Markahofmeister/Whipper-Snapper/figures/cable-diagram-1.png

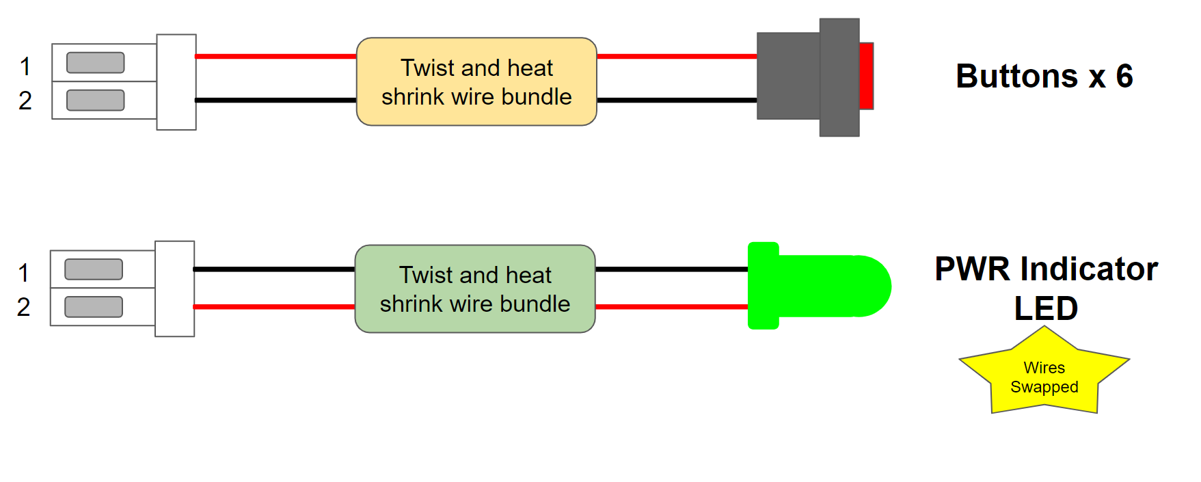
figures/cable-diagram-1.png
