Markahofmeister/Whipper-Snapper/figures/cable-diagram-2.png

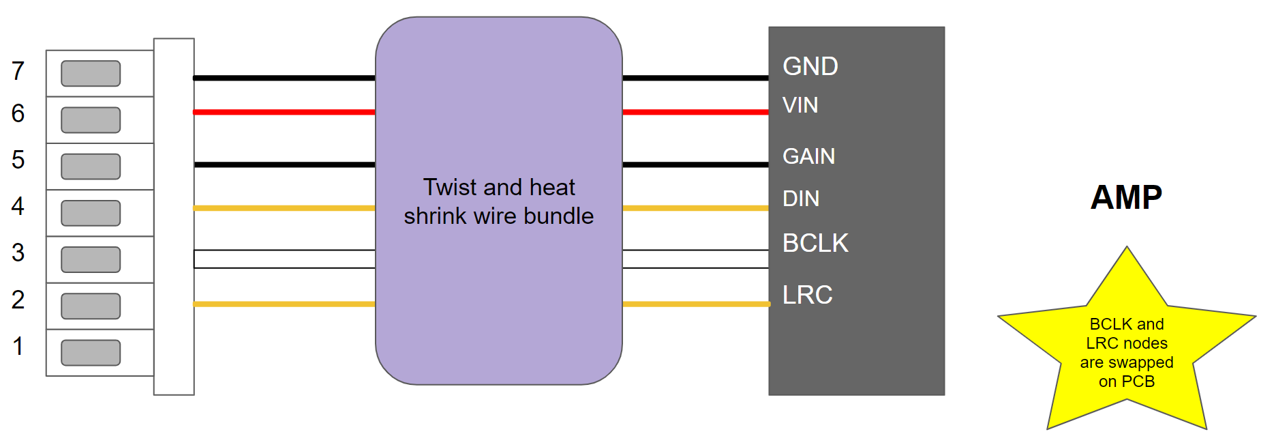
figures/cable-diagram-2.png
