Markahofmeister/Whipper-Snapper/figures/flowchart-interrupts.png

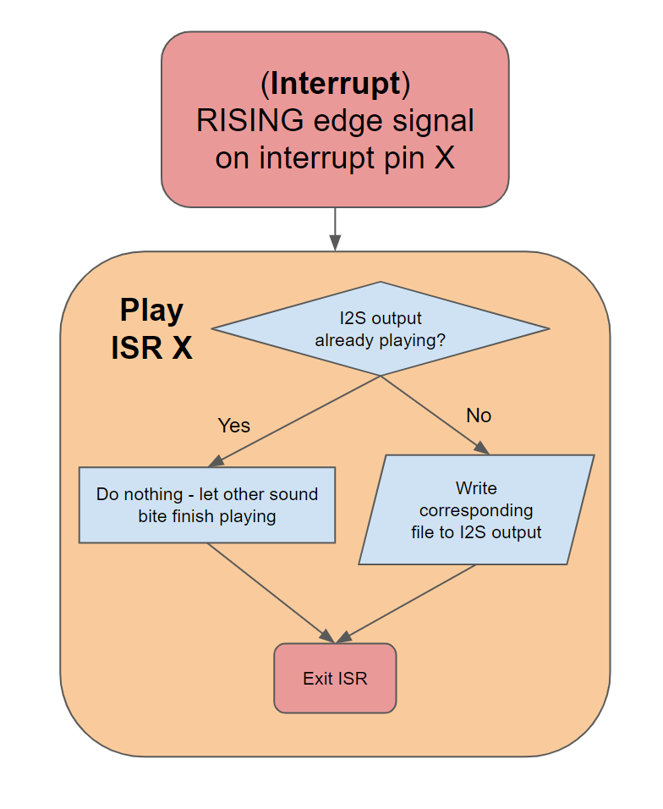
figures/flowchart-interrupts.png
