Markahofmeister/Whipper-Snapper/figures/flowchart-main.png

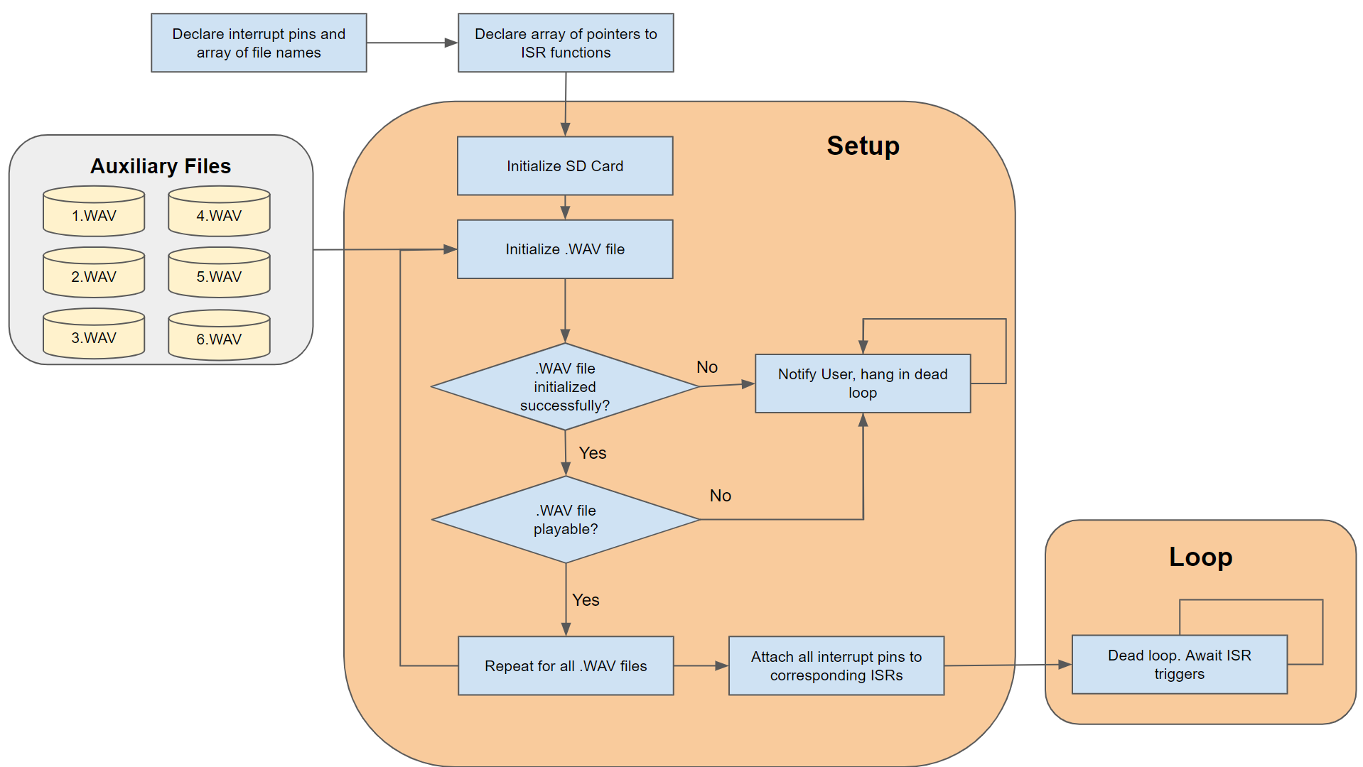
figures/flowchart-main.png
