Markahofmeister/Whipper-Snapper/media/amp.png

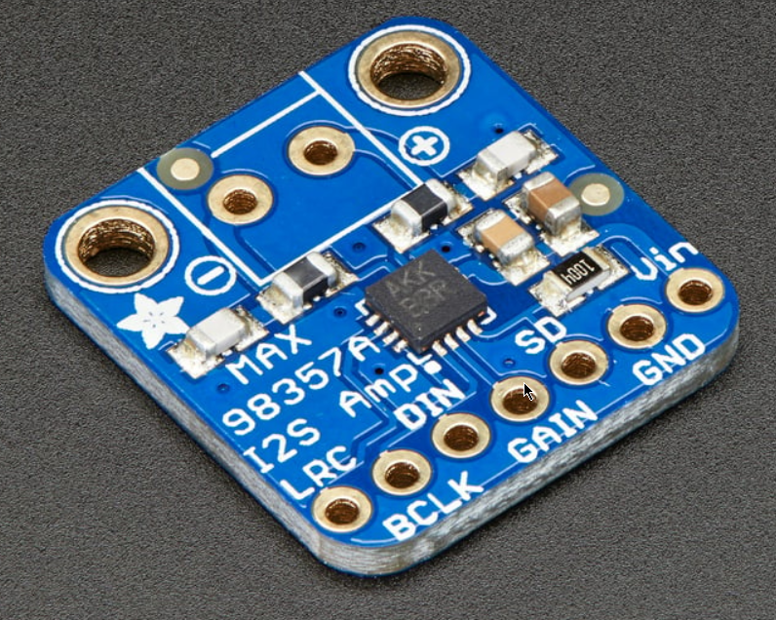
media/amp.png
