Markahofmeister/Whipper-Snapper/media/enclosure-layout-annotated.png

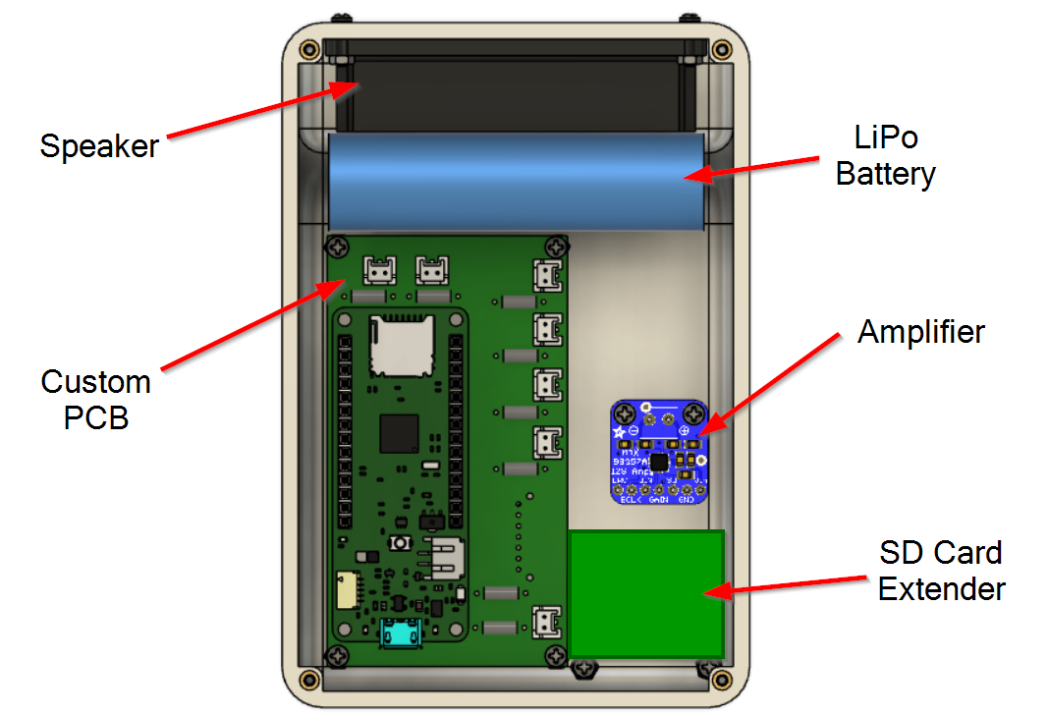
media/enclosure-layout-annotated.png
