Markahofmeister/Whipper-Snapper/media/exploded-view-annotated.png

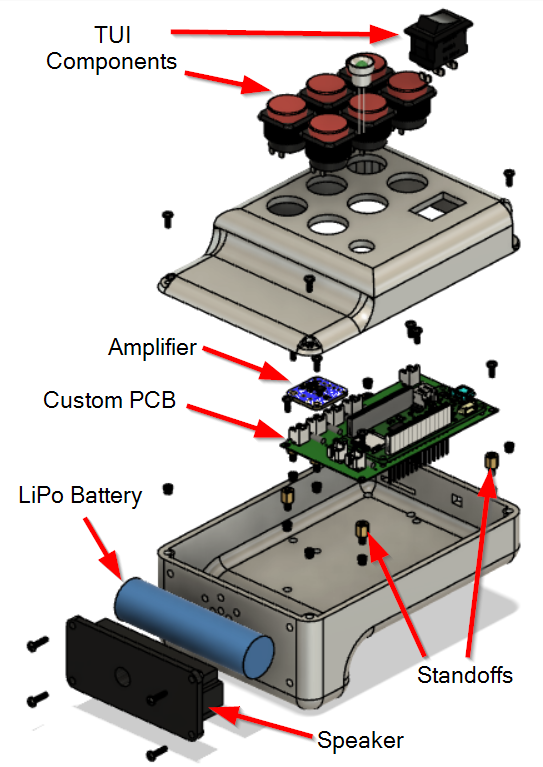
media/exploded-view-annotated.png
