Markahofmeister/Whipper-Snapper/media/final-1.jpg

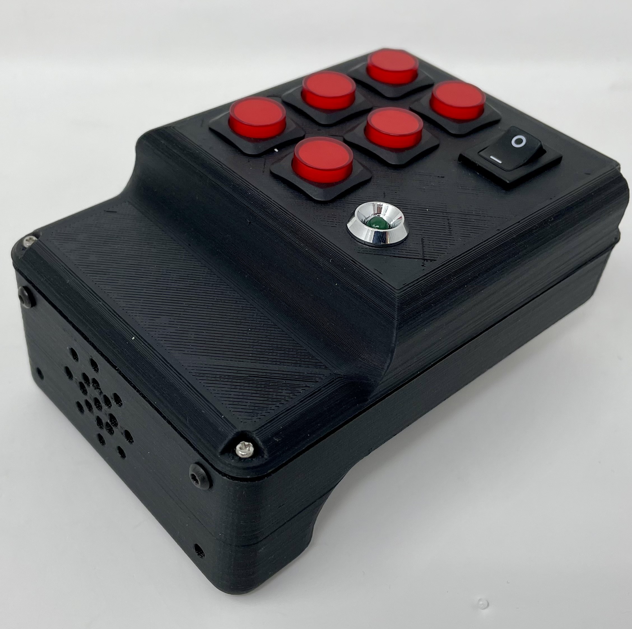
media/final-1.jpg
