Markahofmeister/Whipper-Snapper/media/fritzing.png

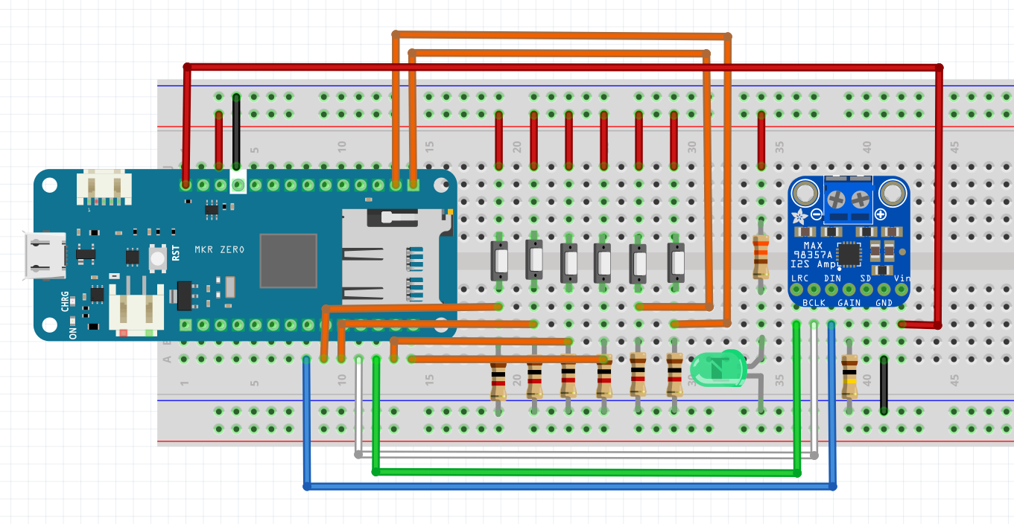
media/fritzing.png
