Markahofmeister/Whipper-Snapper/media/mkr-zero.png

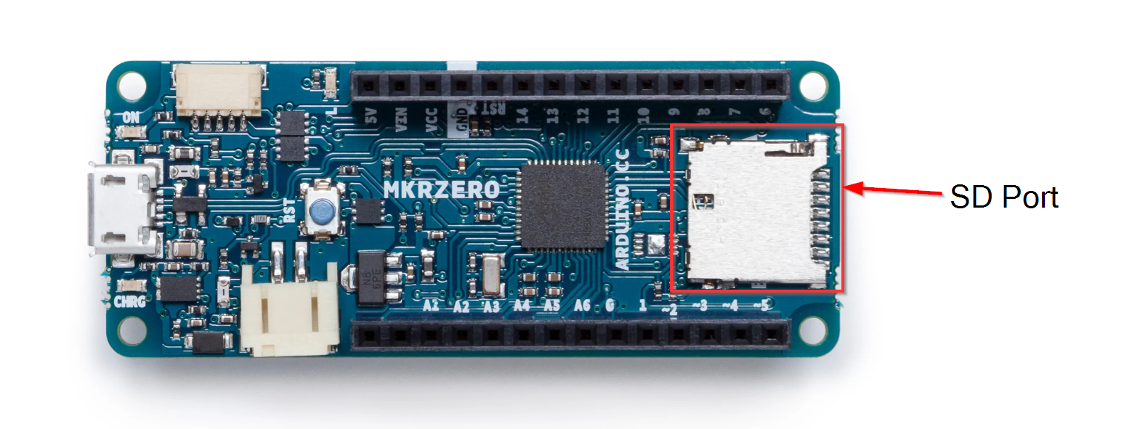
media/mkr-zero.png
