Markahofmeister/Whipper-Snapper/media/pcb-top.png

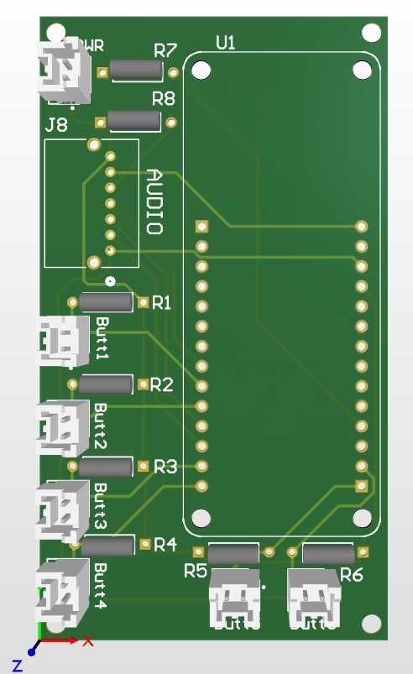
media/pcb-top.png
