Markahofmeister/Whipper-Snapper/media/ratsnest.jpg

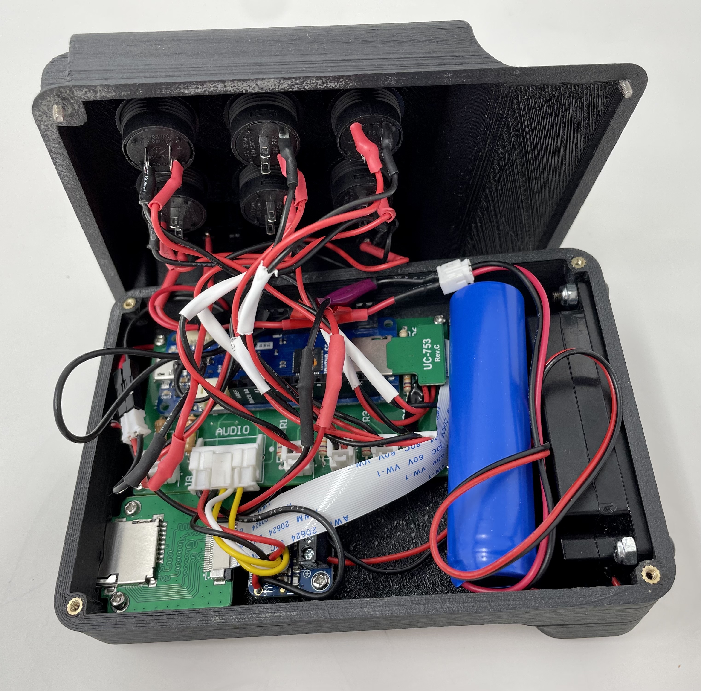
media/ratsnest.jpg
