Markahofmeister/Whipper-Snapper/media/render.png

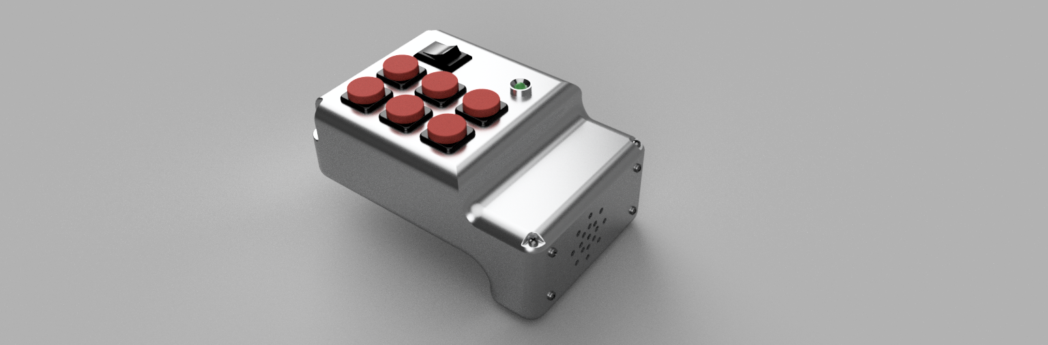
media/render.png
