Markahofmeister/Whipper-Snapper/media/SD-charger.jpg

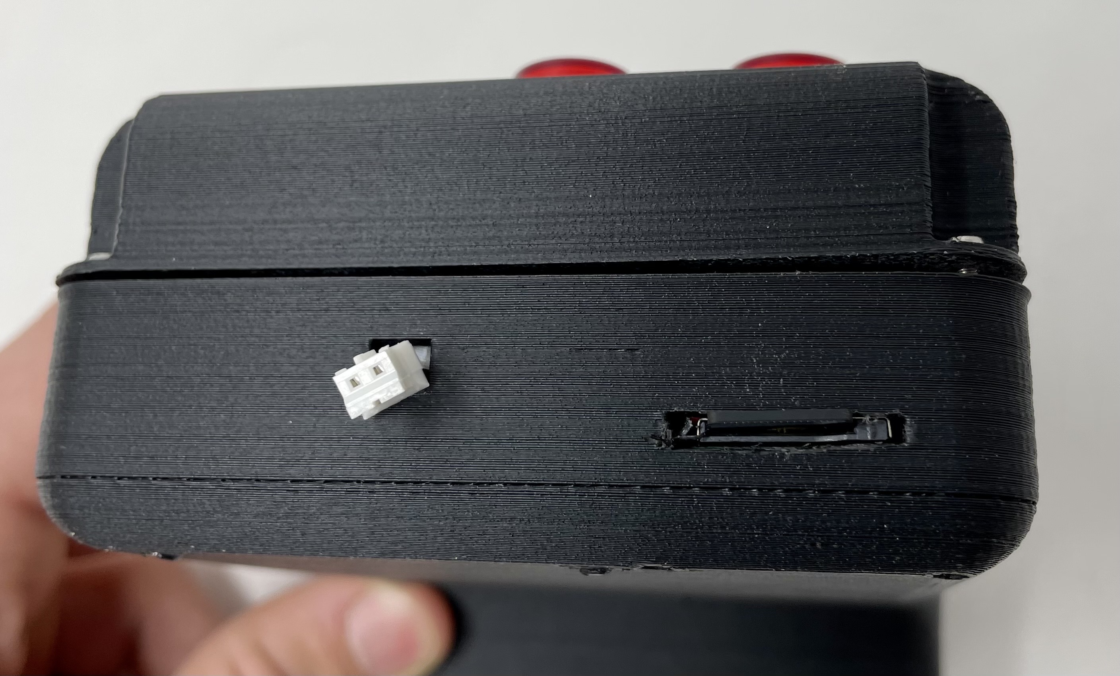
media/SD-charger.jpg
