Markahofmeister/Whipper-Snapper/media/SD-chrger-annotated.png

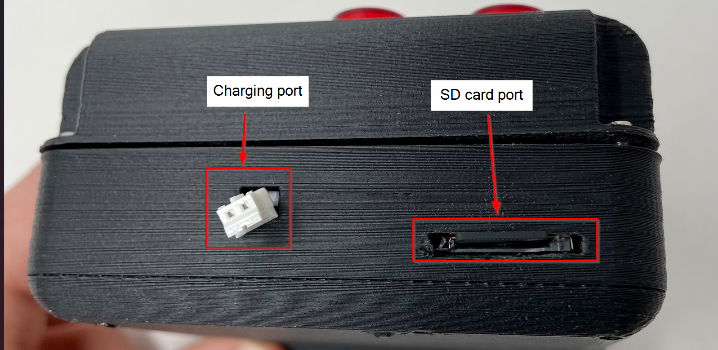
media/SD-chrger-annotated.png
