Markahofmeister/Whipper-Snapper/media/TUI.jpg

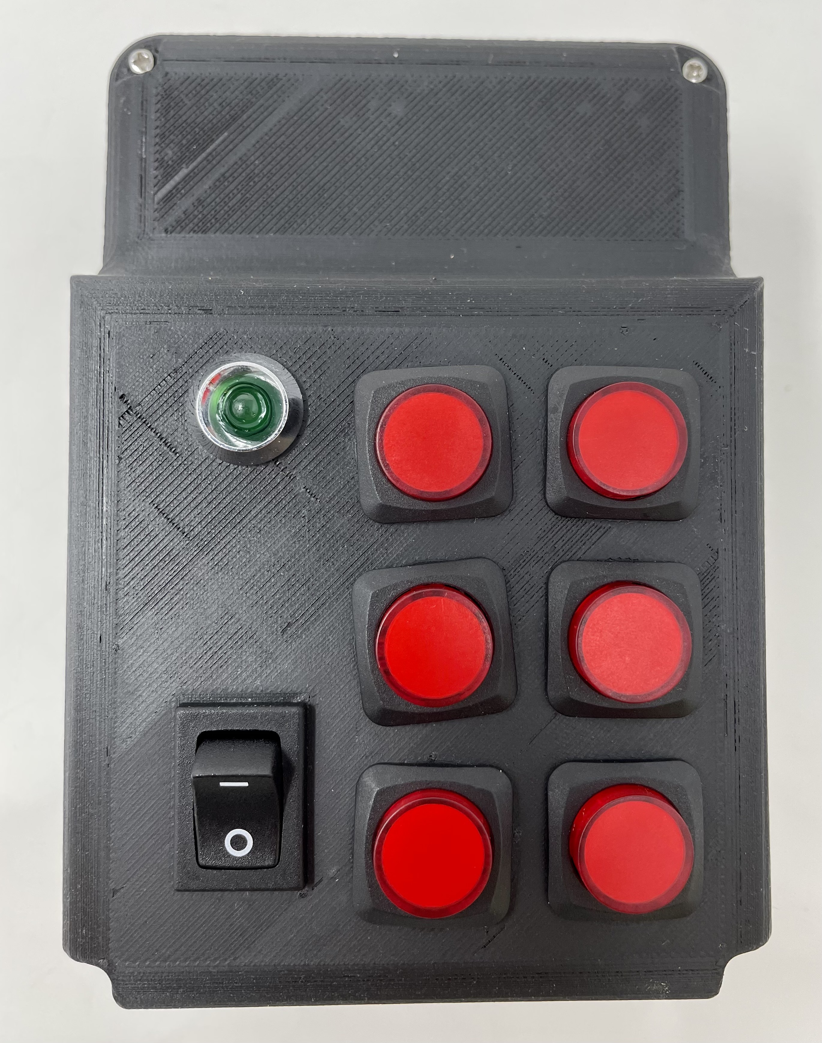
media/TUI.jpg
