Markahofmeister/Whipper-Snapper/media/WHAT.png

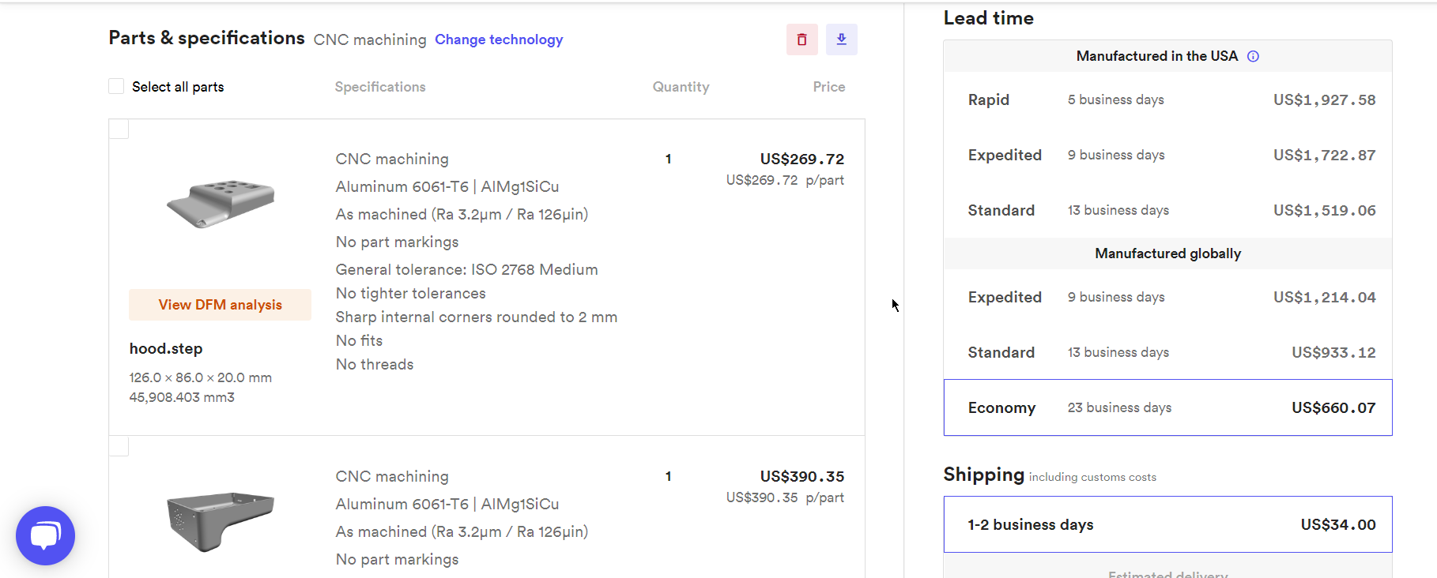
media/WHAT.png
